iostwestcoast/PCB_Controller/Photos & Videos & Screenshots/1.png

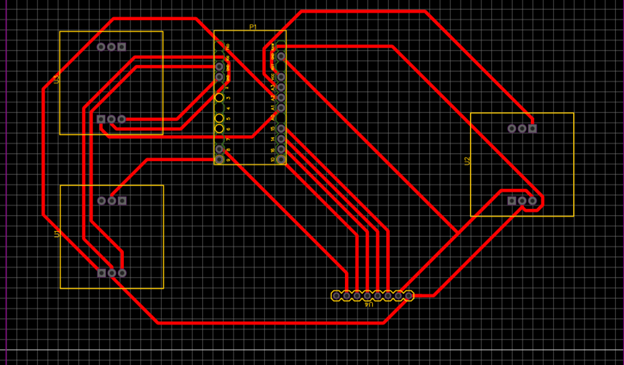
Photos & Videos & Screenshots/1.png
