iostwestcoast/PCB_Controller/Photos & Videos & Screenshots/2.png

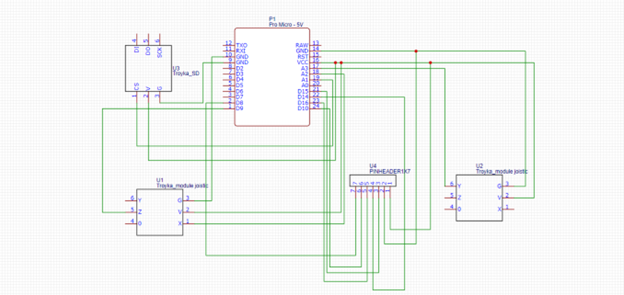
Photos & Videos & Screenshots/2.png
