iostwestcoast/PCB_Controller/Photos & Videos & Screenshots/3.png

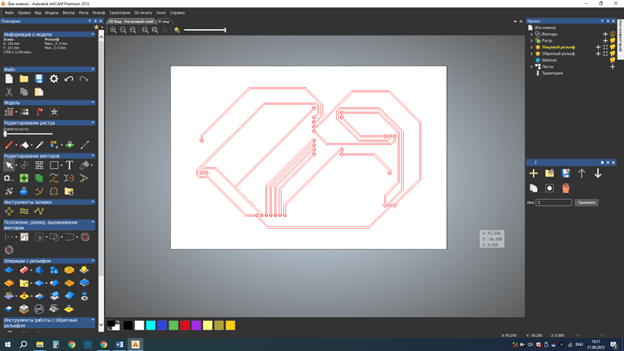
Photos & Videos & Screenshots/3.png
