iostwestcoast/PCB_Controller/Photos & Videos & Screenshots/4.png

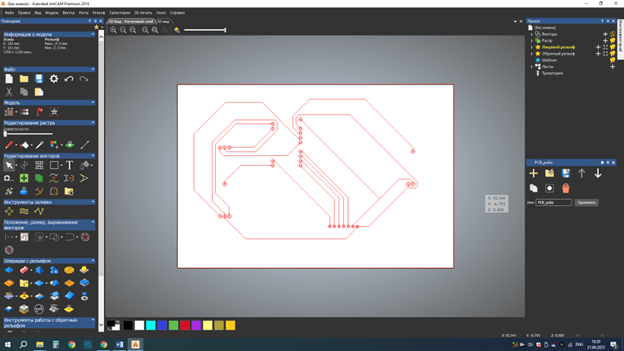
Photos & Videos & Screenshots/4.png
