iostwestcoast/PCB_Controller/Photos & Videos & Screenshots/5.png

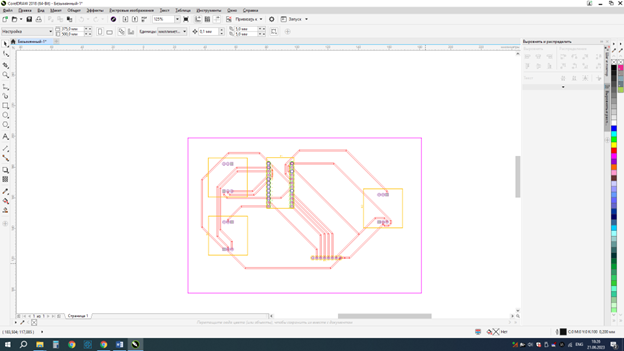
Photos & Videos & Screenshots/5.png
