iostwestcoast/PCB_Controller/Photos & Videos & Screenshots/6.png

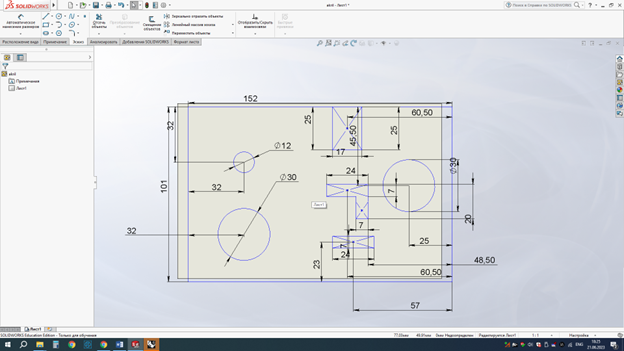
Photos & Videos & Screenshots/6.png
