iostwestcoast/PCB_Controller/Photos & Videos & Screenshots/7.png

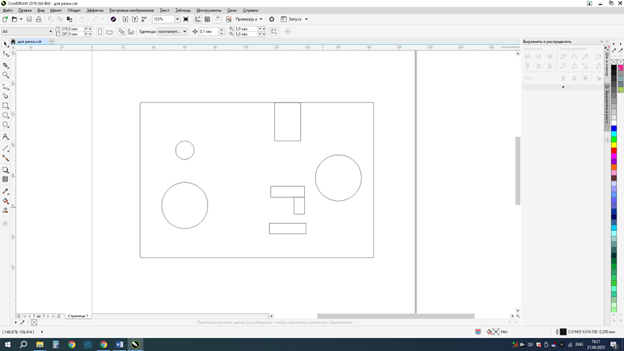
Photos & Videos & Screenshots/7.png
