iostwestcoast/PCB_Controller/Photos & Videos & Screenshots/8.png

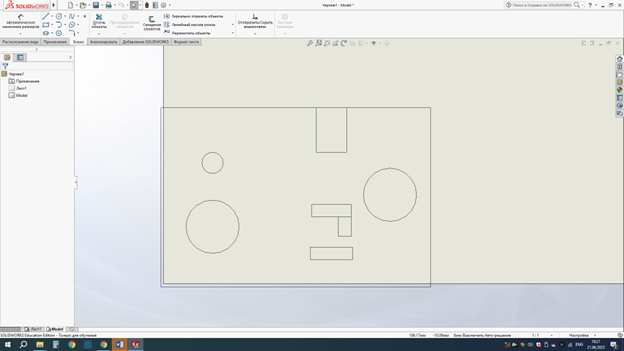
Photos & Videos & Screenshots/8.png
