iostwestcoast/PCB_Controller/Photos & Videos & Screenshots/photo_2023-06-23_14-38-38.jpg

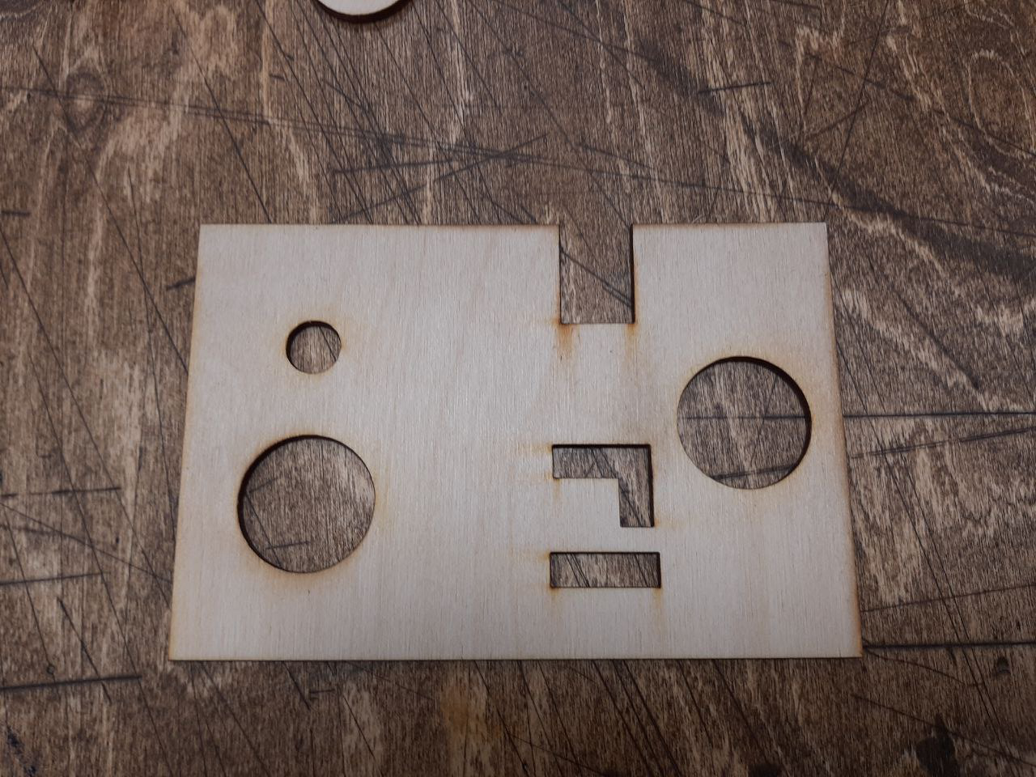
Photos & Videos & Screenshots/photo_2023-06-23_14-38-38.jpg
