iostwestcoast/PCB_Controller/Photos & Videos & Screenshots/photo_2023-06-23_14-39-04.jpg

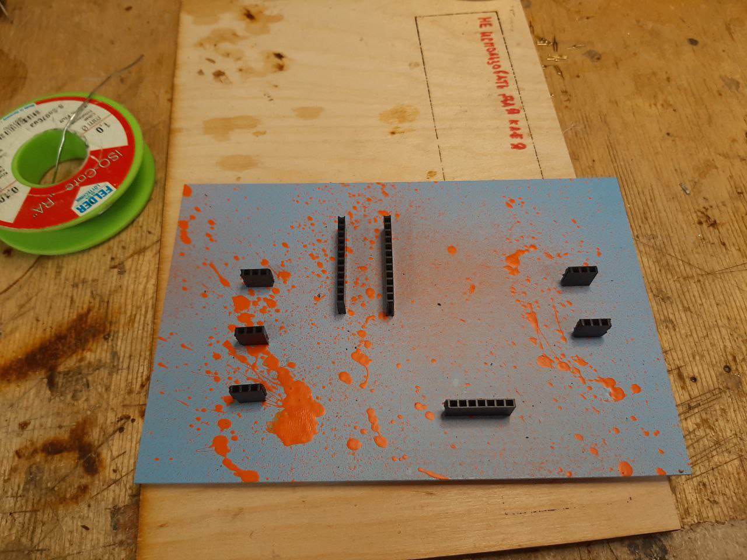
Photos & Videos & Screenshots/photo_2023-06-23_14-39-04.jpg
